MBW0lf/RCJ-Soccer-Lightweight-2020/PCB/Top Layer/1.png

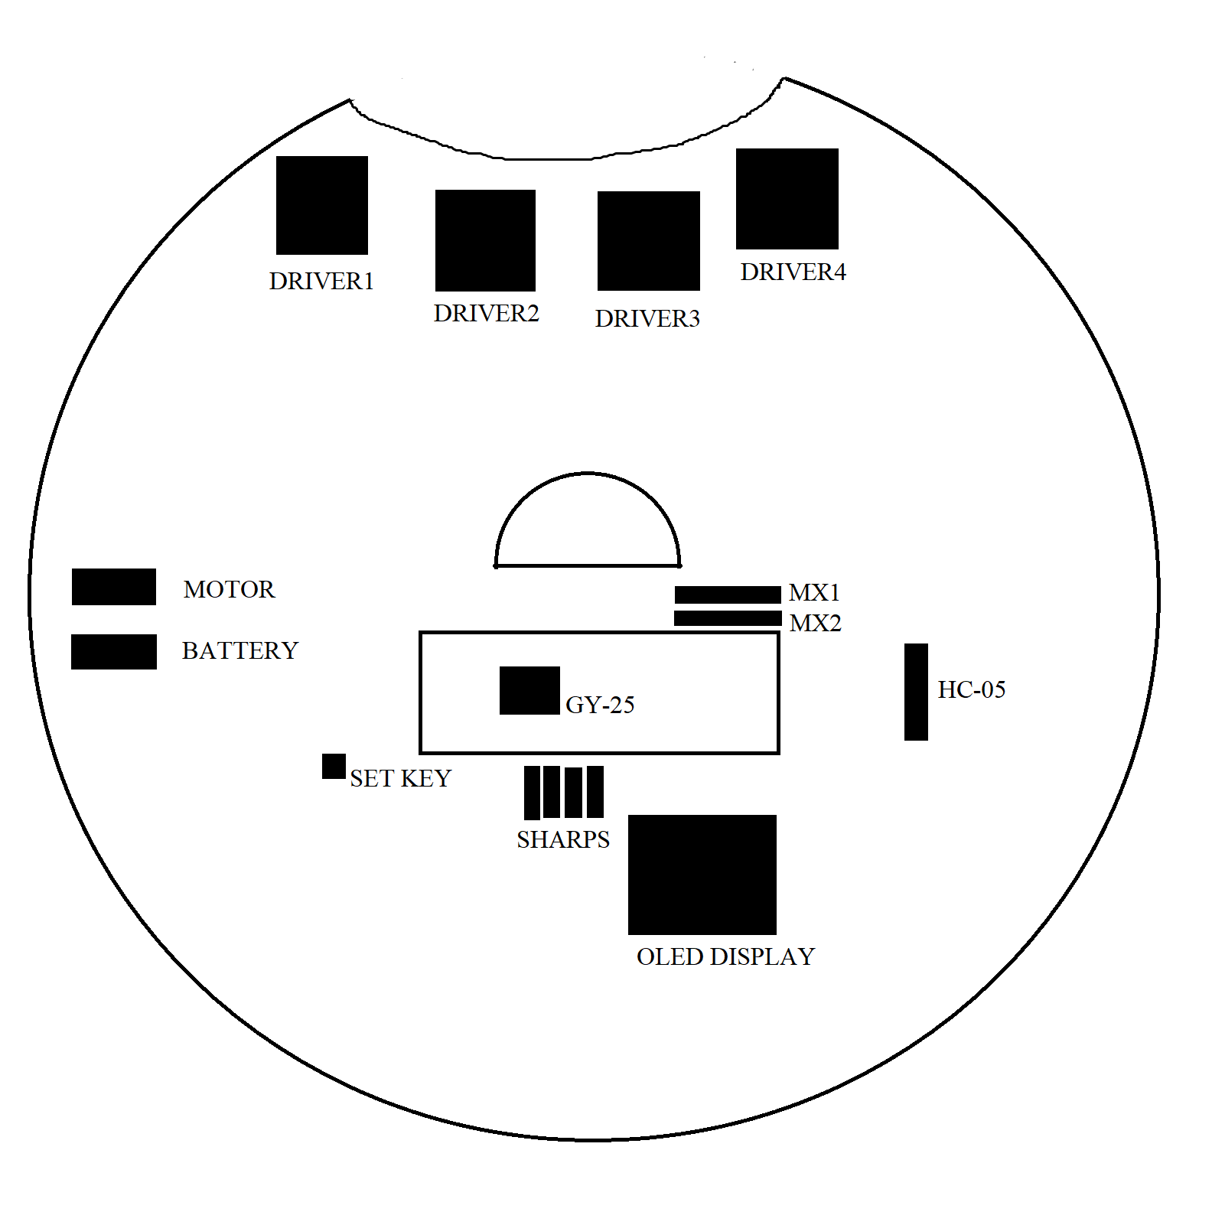
PCB/Top Layer/1.png
